bogd/esp32-morphing-clock/case/photos/2021-04-21 19.40.15.jpg

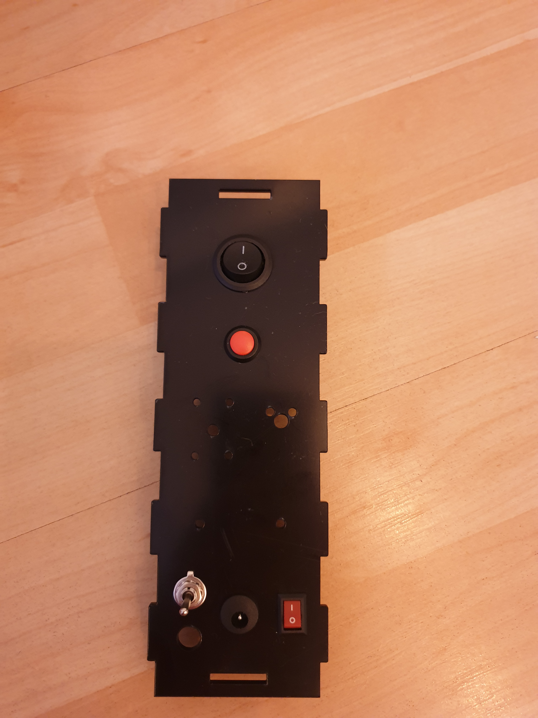
case/photos/2021-04-21 19.40.15.jpg
