bogd/esp32-morphing-clock/pcb/photos/gerber-front.png

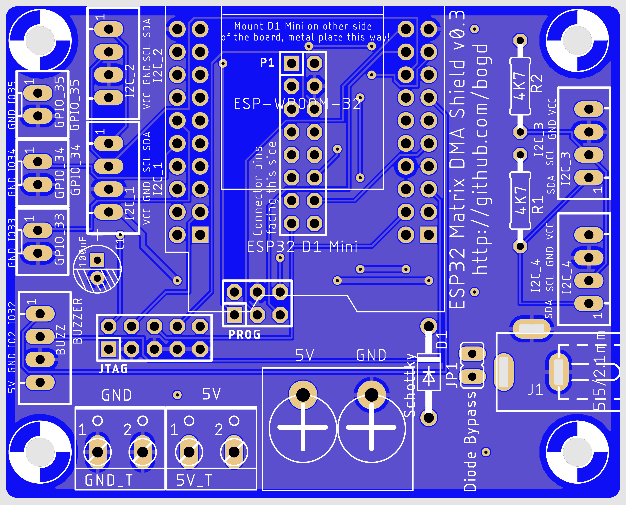
pcb/photos/gerber-front.png
