bogd/esp32-morphing-clock/pcb/photos/assembled_back.jpg

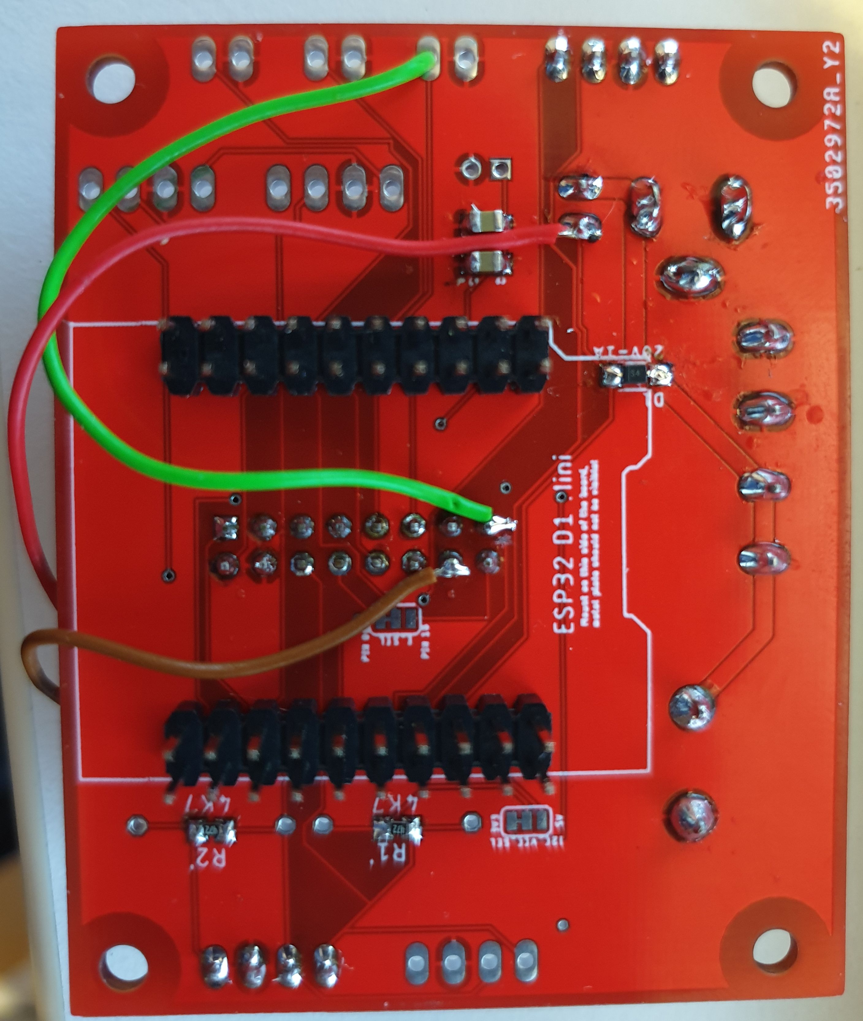
pcb/photos/assembled_back.jpg
