bogd/esp32-morphing-clock/pcb/photos/assembled_front.jpg

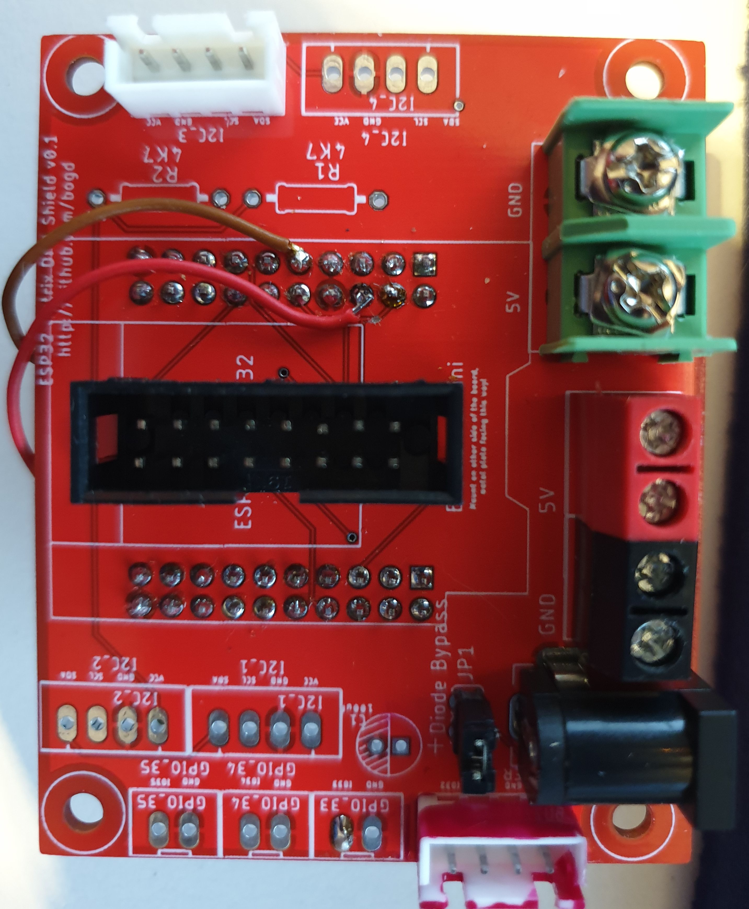
pcb/photos/assembled_front.jpg
