bogd/esp32-morphing-clock/code/include/weather.h

#ifndef WEATHER_H
#define WEATHER_H

#include <Arduino.h>

void displaySensorData();
void drawTestBitmap();
void displayTodaysWeather();
void displayWeatherForecast();
void displayWeatherData();
void displayTodaysTempRange();
void drawHeartBeat();
void drawBitmap(int startx, int starty, int width, int height, uint32_t *bitmap);
void drawBitmap(int startx, int starty, int width, int height, uint32_t *bitmap, bool enlarged);
void getAccuWeatherData();

#endif
